Arnoud-Whizzbizz/retrophone/Images/removing-microsd-card.jpeg

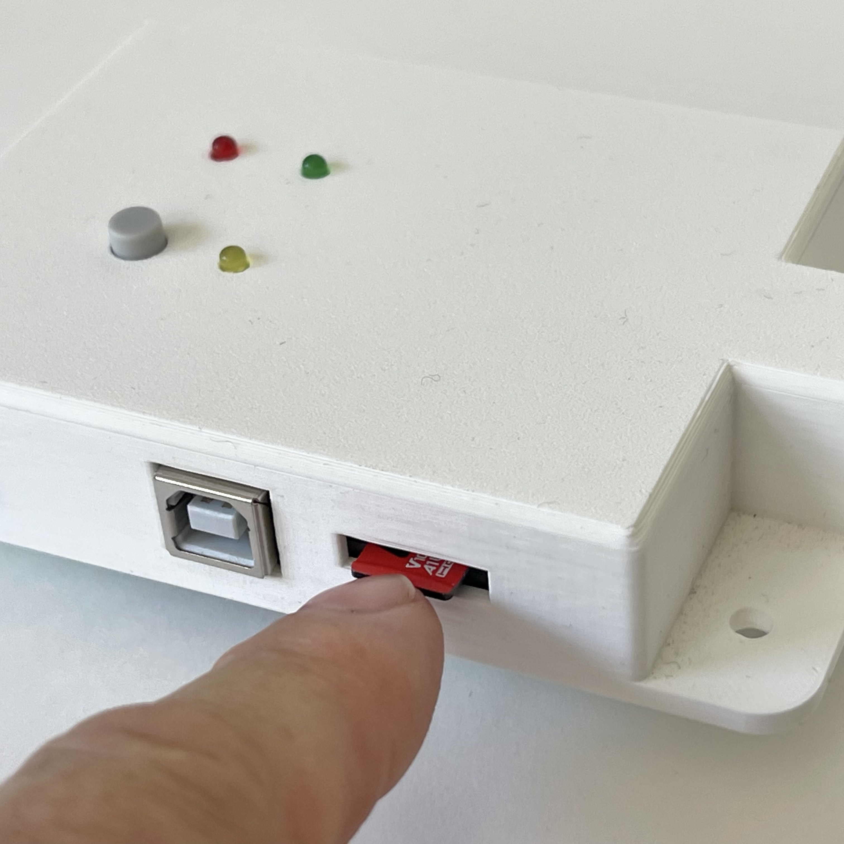
Images/removing-microsd-card.jpeg
